Sylaina/VW-Kaefer-Spannungskonstanter-Ersatz/src/FloatingAverage.c

#include "FloatingAverage.h"

void InitFloatAvg(tFloatAvgFilter * io_pFloatAvgFilter, 
		  tFloatAvgType i_DefaultValue)
{ 
 	// Den Buffer mit dem Initialisierungswert fuellen:
	for (uint8_t i = 0; i < SIZE_OF_AVG; ++i)
	{
		io_pFloatAvgFilter->aData[i] = i_DefaultValue;
	}
	// Der naechste Wert soll an den Anfang des Buffers geschrieben werden:
	io_pFloatAvgFilter->IndexNextValue = 0;
} 


void AddToFloatAvg(tFloatAvgFilter * io_pFloatAvgFilter,
		   tFloatAvgType i_NewValue)
{ 
	// Neuen Wert an die dafuer vorgesehene Position im Buffer schreiben.
	io_pFloatAvgFilter->aData[io_pFloatAvgFilter->IndexNextValue] =
		i_NewValue;
	// Der naechste Wert wird dann an die Position dahinter geschrieben.
	io_pFloatAvgFilter->IndexNextValue++;
	// Wenn man hinten angekommen ist, vorne wieder anfangen.
	io_pFloatAvgFilter->IndexNextValue %= SIZE_OF_AVG;
}  


tFloatAvgType GetOutputValue(tFloatAvgFilter * io_pFloatAvgFilter)
{
	tTempSumType TempSum = 0;
	// Durchschnitt berechnen
	for (uint8_t i = 0; i < SIZE_OF_AVG; ++i)
	{
		TempSum += io_pFloatAvgFilter->aData[i];
	}
	// Der cast is OK, wenn tFloatAvgType und tTempSumType korrekt gewaehlt wurden.
	tFloatAvgType o_Result = (tFloatAvgType) (TempSum / SIZE_OF_AVG);
	return o_Result;
}
